cwi-dis/volvo/photon-experiment/schematic.jpg

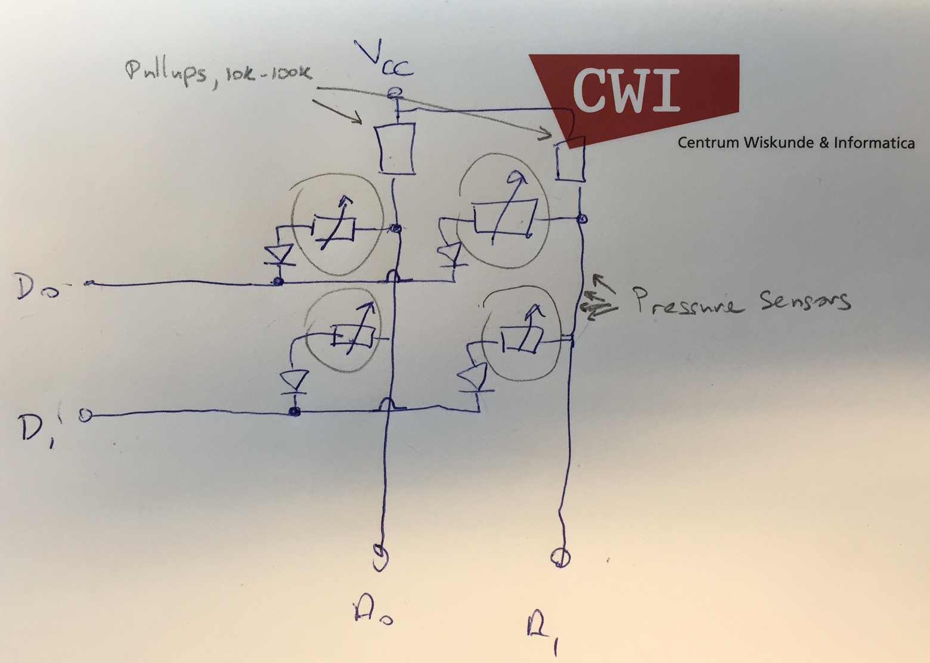
photon-experiment/schematic.jpg
