cwi-dis/volvo/hwsetup/IMG_0008.jpg

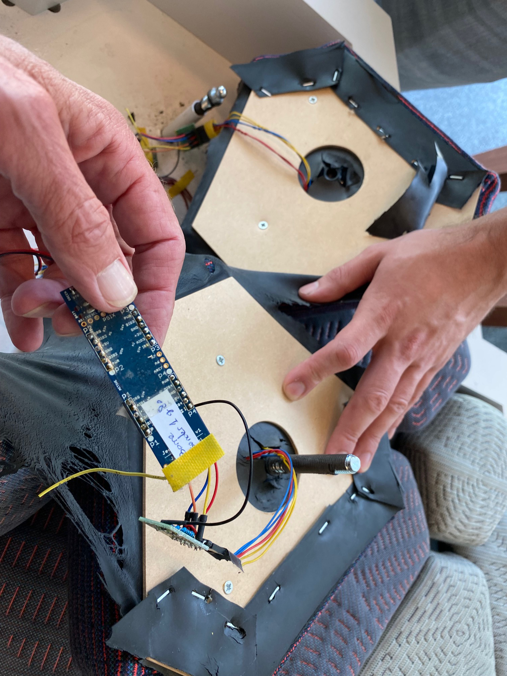
hwsetup/IMG_0008.jpg
