cwi-dis/volvo/hwsetup/IMG_0010.jpg

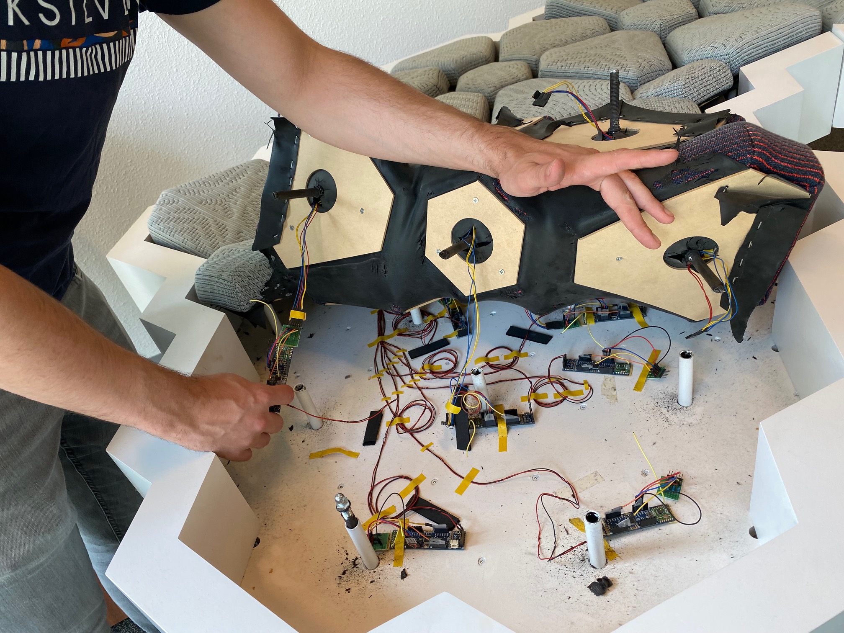
hwsetup/IMG_0010.jpg
