cwi-dis/volvo/hwsetup/IMG_0011.jpg

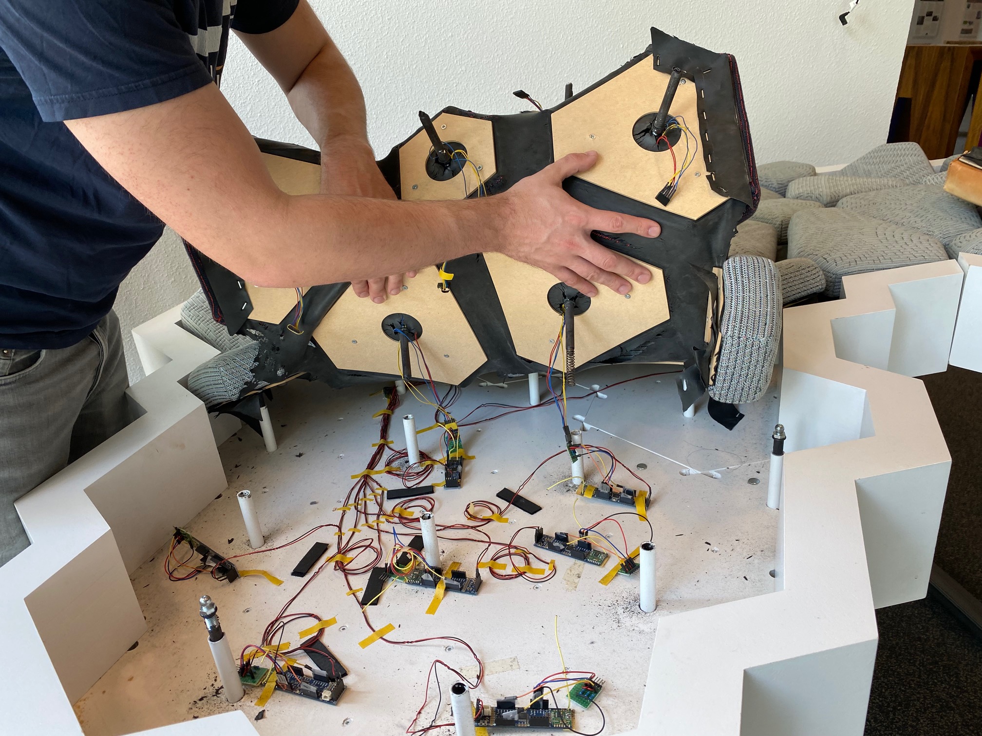
hwsetup/IMG_0011.jpg
