cwi-dis/volvo/hwsetup/IMG_0017.jpg

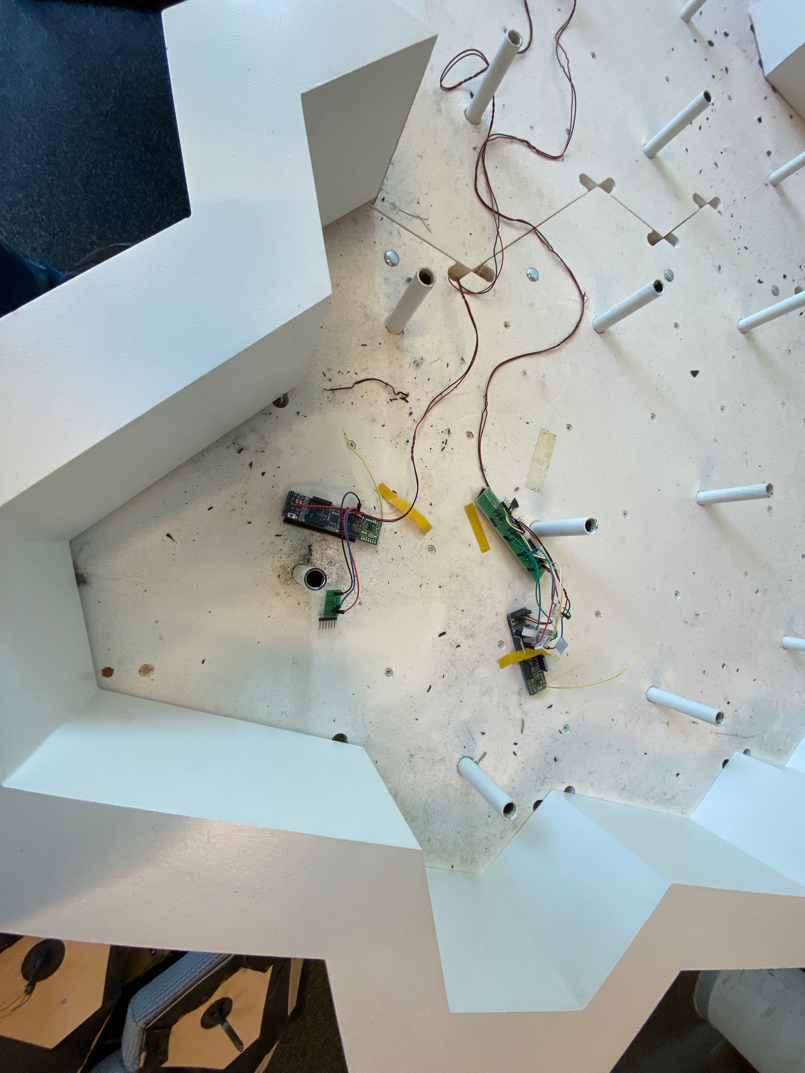
hwsetup/IMG_0017.jpg
