cwi-dis/volvo/hwsetup/IMG_0019.jpg

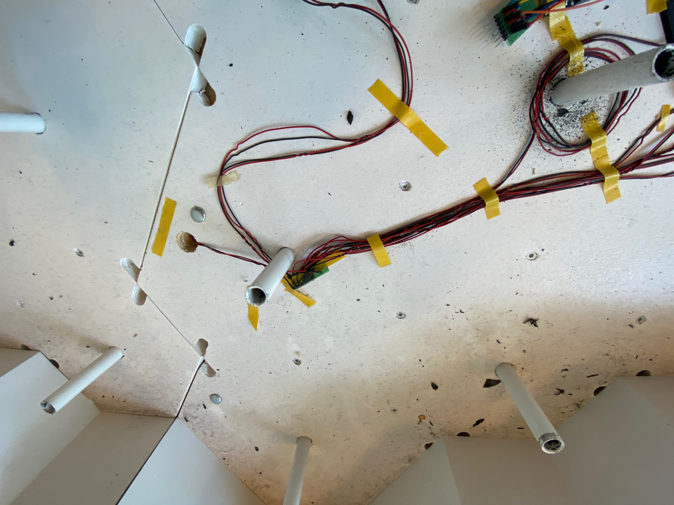
hwsetup/IMG_0019.jpg
